Beserrovsky/britcinn/floorplan/FLOORPLAN_PSI.png

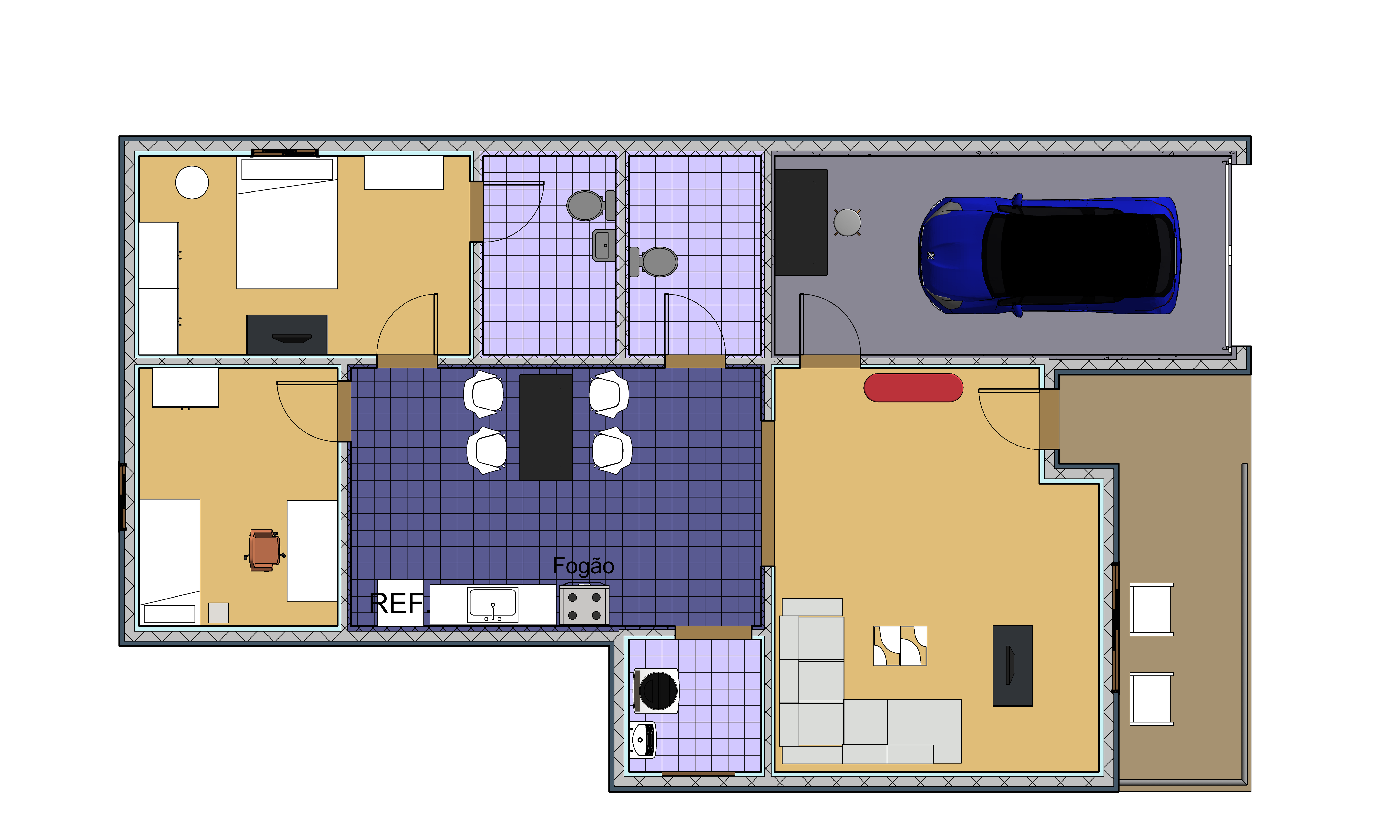
floorplan/FLOORPLAN_PSI.png
