Beserrovsky/britcinn/eletronics/britcinn_eletronics.kicad_pcb

## KiCad design Proyecto/ModuloElectrónico/Esquema sensores 1.1/schematic.kicad_sch

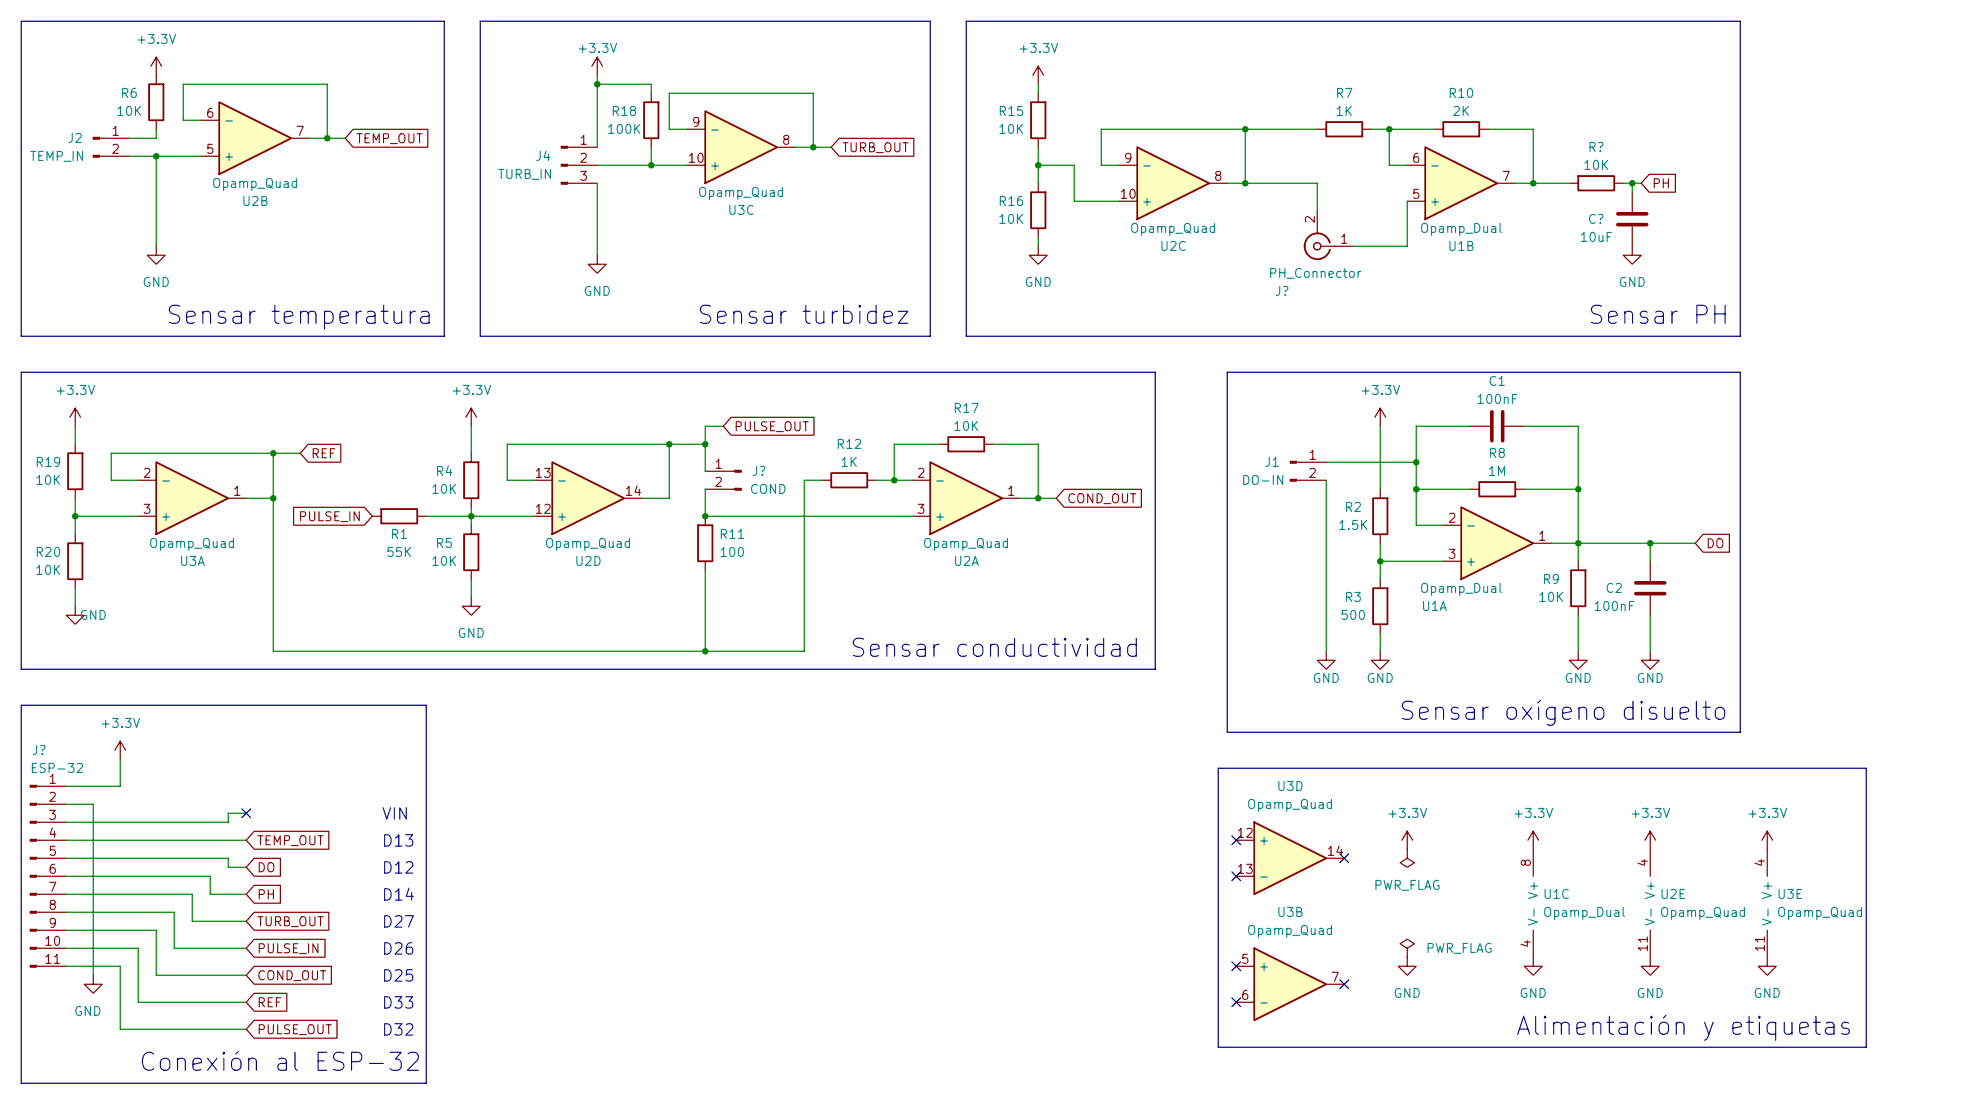
[picture p19: schematic schematic.kicad_sch]

Parts:
C1, C2: 100nF
J1: DO-IN
J2: TEMP_IN
J4: TURB_IN
R1: 55K
R2: 1.5K
R3: 500
R4, R5, R6, R9, R15, R16, R17, R19, R20: 10K
R7, R12: 1K
R8: 1M
R10: 2K
R11: 100
R18: 100K
U1: Opamp_Dual
U2, U3: Opamp_Quad

Connections:
+3.3V: J4.1, R2.2, R4.2, R6.2, R18.2, R19.2, U1.8 (V+), U2.4 (V+), U3.4 (V+)
COND_OUT: R17.2, U2.1
DO: C1.2, C2.2, R8.2, R9.2, U1.1
GND: C2.1, J1.2, J2.2, J4.3, R3.1, R5.1, R9.1, R16.1, R20.1, U1.4 (V-), U2.5 (+), U2.11 (V-), U3.11 (V-)
unnamed: C1.1, J1.1, R8.1, U1.2 (-)
unnamed: J2.1, R6.1
unnamed: J4.2, R18.1, U3.10 (+)
unnamed: R1.1, R4.1, R5.2, U2.12 (+)
unnamed: R2.1, R3.2, U1.3 (+)
unnamed: R7.1, U2.8, U2.9 (-)
unnamed: R7.2, R10.1, U1.6 (-)
unnamed: R10.2, U1.7
unnamed: R11.2, U2.3 (+)
unnamed: R12.2, R17.1, U2.2 (-)
unnamed: R15.1, R16.2, U2.10 (+)
unnamed: R19.1, R20.2, U3.3 (+)
PULSE_IN: R1.2
PULSE_OUT: U2.13 (-), U2.14
REF: R11.1, R12.1, U3.1, U3.2 (-)
TEMP_OUT: U2.6 (-), U2.7
TURB_OUT: U3.8, U3.9 (-)

Notes on the sheet:
D26
Sensar oxígeno disuelto
Sensar turbidez
D13
D12
D25
D27
Sensar temperatura
Sensar conductividad
Alimentación y etiquetas
Conexión al ESP-32
Sensar PH
D32
D33
D14
VIN
